A0Cybernetics/ID-01/Documents/buildGuidePictures/electronics1.jpg

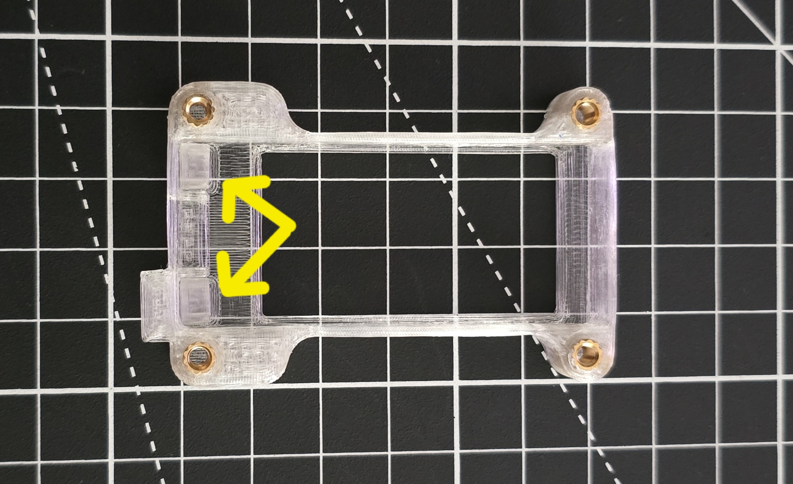
Documents/buildGuidePictures/electronics1.jpg
