A0Cybernetics/ID-01/Documents/buildGuidePictures/electronics4.jpg

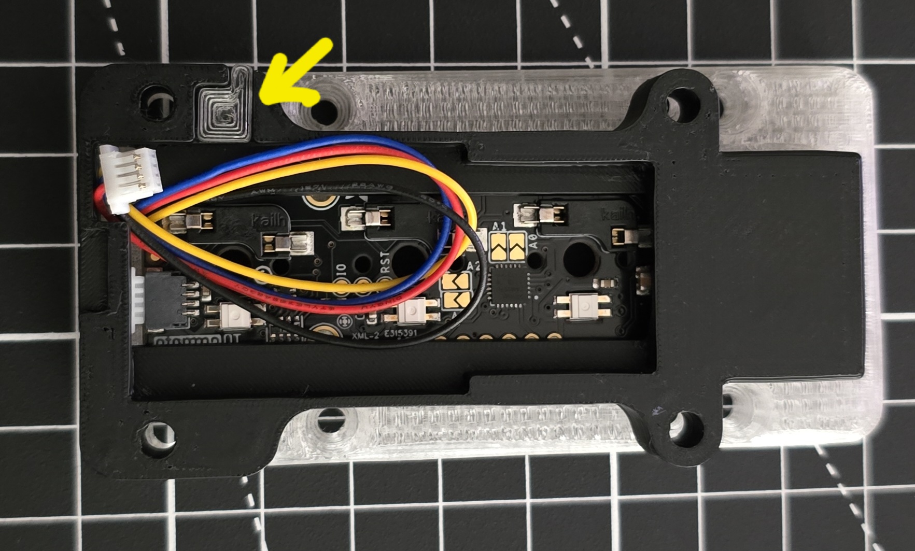
Documents/buildGuidePictures/electronics4.jpg
