A0Cybernetics/ID-01/Documents/buildGuidePictures/electronics5.jpg

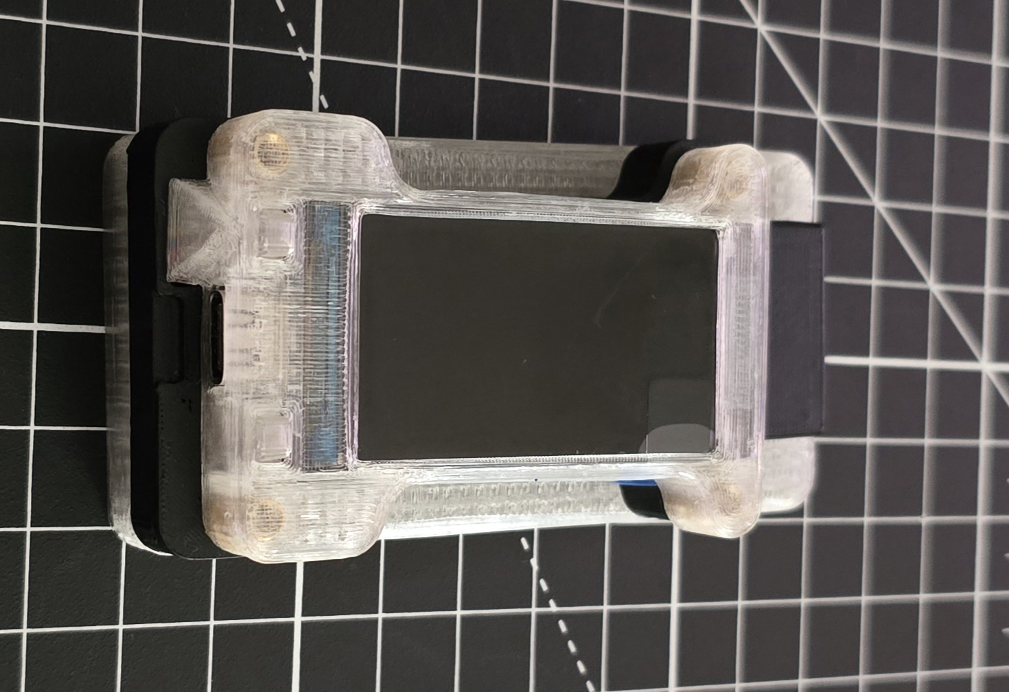
Documents/buildGuidePictures/electronics5.jpg
