A0Cybernetics/ID-01/Documents/buildGuidePictures/electronics6.jpg

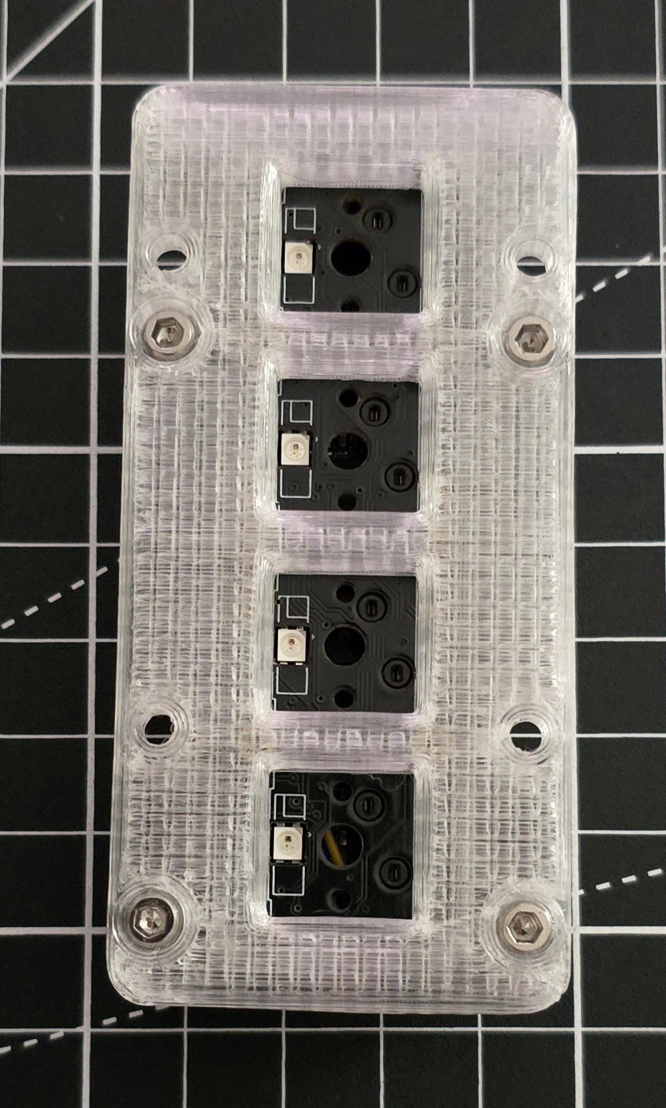
Documents/buildGuidePictures/electronics6.jpg
