A0Cybernetics/ID-01/Documents/READMEPics/led.jpg

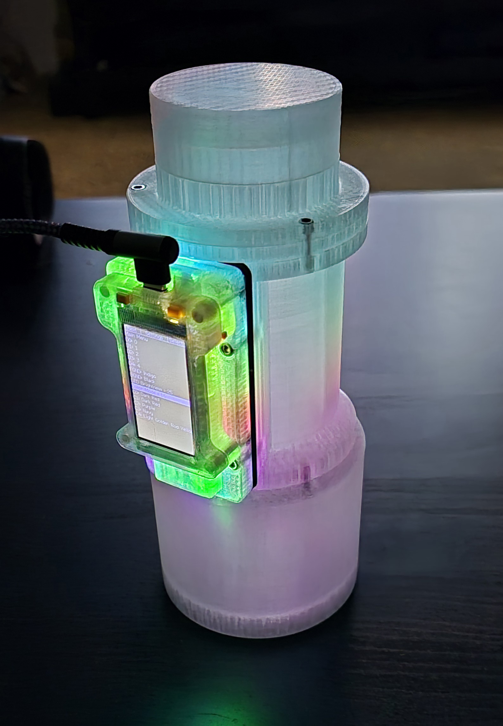
Documents/READMEPics/led.jpg
