A0Cybernetics/ID-01/3DModels/V1.0/Adapters-MFleshlight/endPieceFleshlightV1.0-67mm.FCStd

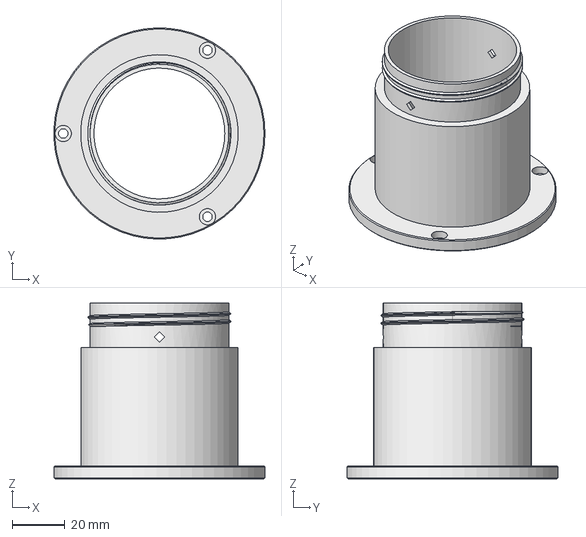
[picture p28: CAD file, 2024-03-15]
3DModels/V1.0/Adapters-MFleshlight/endPieceFleshlightV1.0-67mm.FCStd
80.3 x 80.4 x 67.0 mm
