A0Cybernetics/ID-01/3DModels/V1.0/Buttons/resetButtonV1.0.FCStd

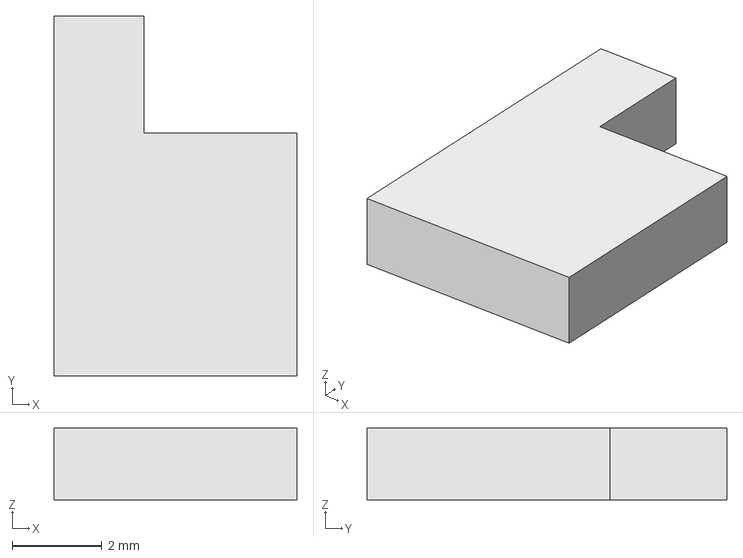
[picture p29: CAD file, 2024-03-15]
3DModels/V1.0/Buttons/resetButtonV1.0.FCStd
5.40 x 8.00 x 1.60 mm
