A0Cybernetics/ID-01/3DModels/V1.0/KeyPlateSpacers/keyPlateSpacerV1.0-1mm.FCStd

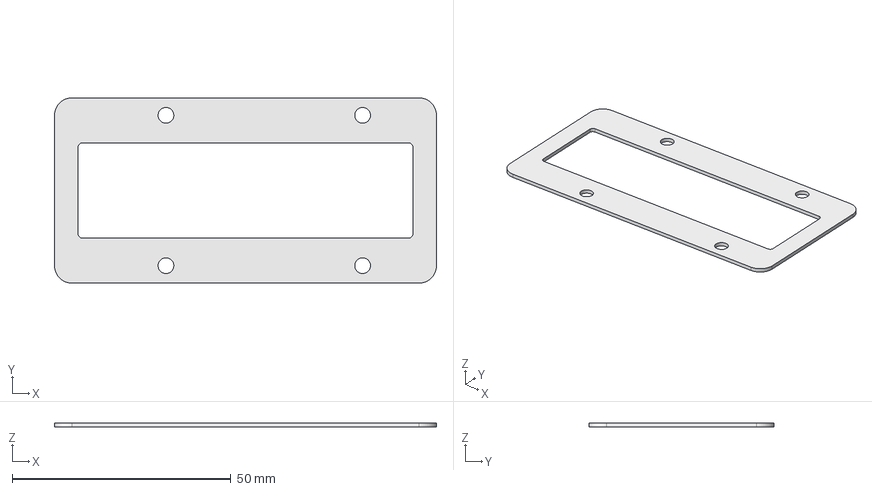
[picture p30: CAD file, 2024-03-15]
3DModels/V1.0/KeyPlateSpacers/keyPlateSpacerV1.0-1mm.FCStd
87.4 x 42.4 x 1.00 mm
