A0Cybernetics/ID-01/3DModels/V1.0/Adapters-FleshlightEndCaps/flEndCapV1.0.FCStd

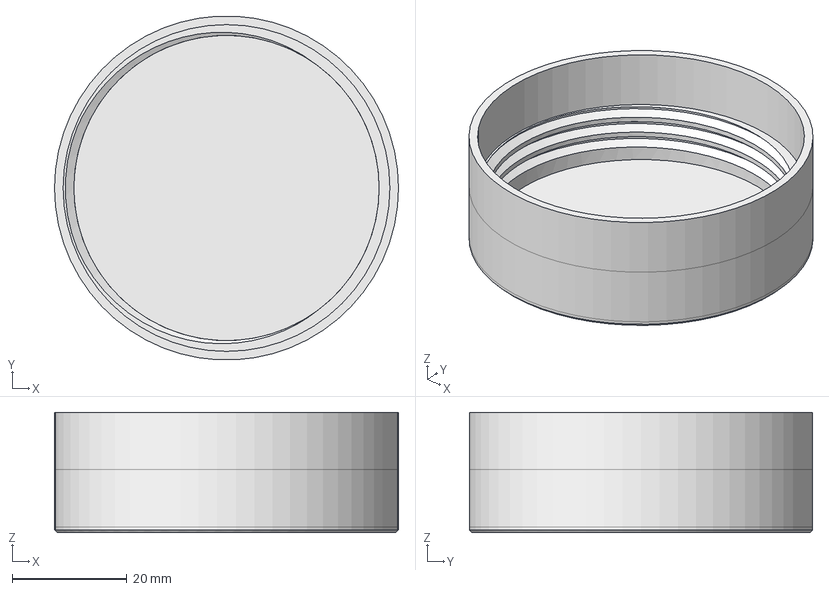
[picture p31: CAD file, 2024-03-15]
3DModels/V1.0/Adapters-FleshlightEndCaps/flEndCapV1.0.FCStd
60.0 x 59.9 x 21.0 mm
