A0Cybernetics/ID-01/3DModels/V1.0/KeyPlateSpacers/keyPlateSpacerV1.0-2mm.FCStd

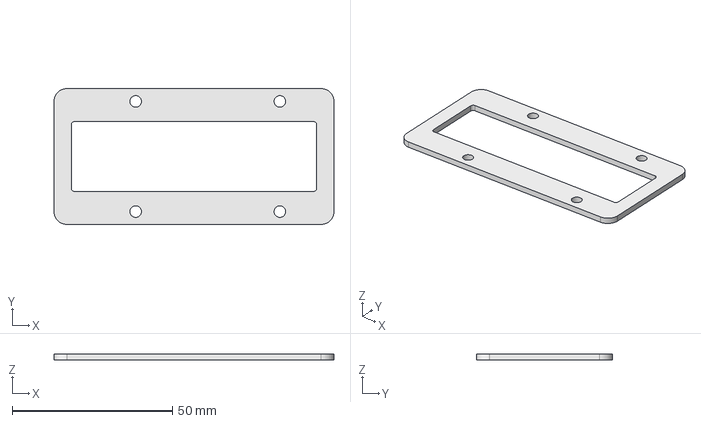
[picture p32: CAD file, 2024-03-15]
3DModels/V1.0/KeyPlateSpacers/keyPlateSpacerV1.0-2mm.FCStd
87.4 x 42.4 x 2.00 mm
