A0Cybernetics/ID-01/3DModels/V1.0/Stabilizers/stabilizerV1.0-50mm.FCStd

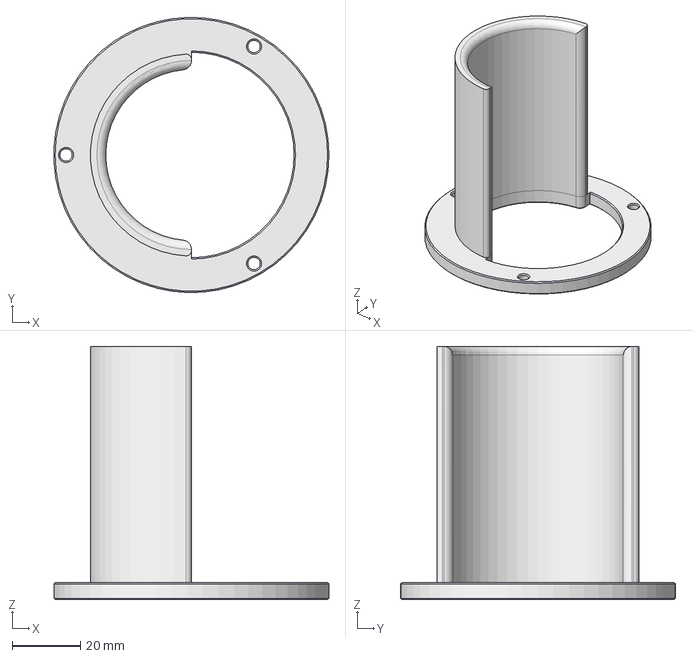
[picture p33: CAD file, 2024-03-15]
3DModels/V1.0/Stabilizers/stabilizerV1.0-50mm.FCStd
80.3 x 80.4 x 74.0 mm
