A0Cybernetics/ID-01/Documents/buildGuidePictures/adjustment2.jpg

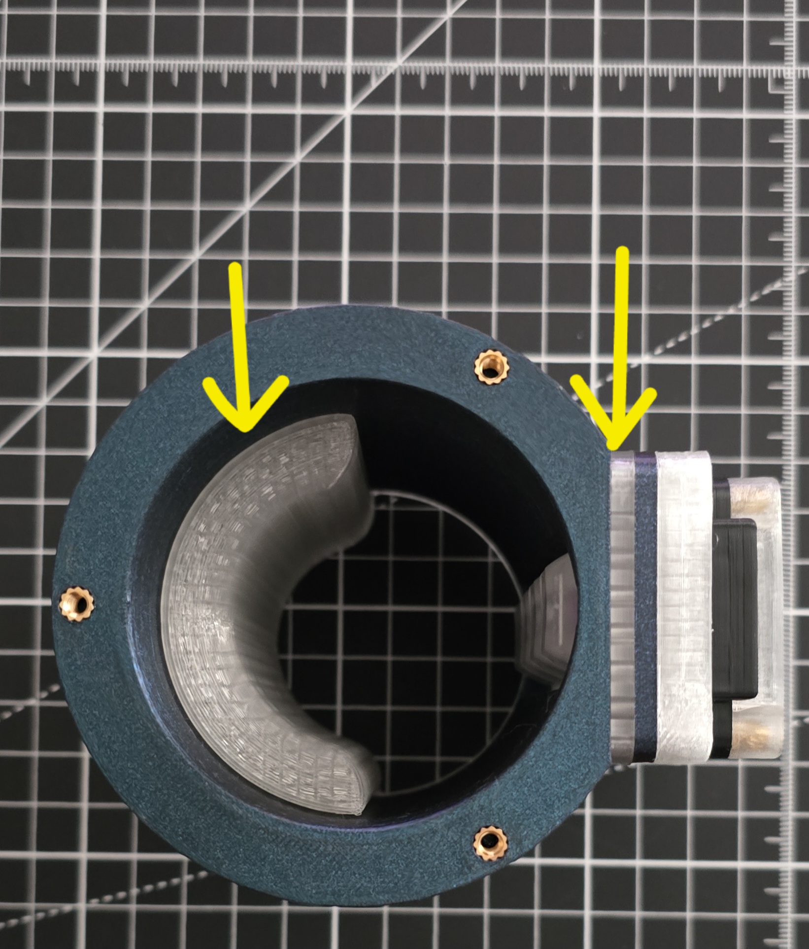
Documents/buildGuidePictures/adjustment2.jpg
