A0Cybernetics/ID-01/Documents/buildGuidePictures/adjustmet1.jpg

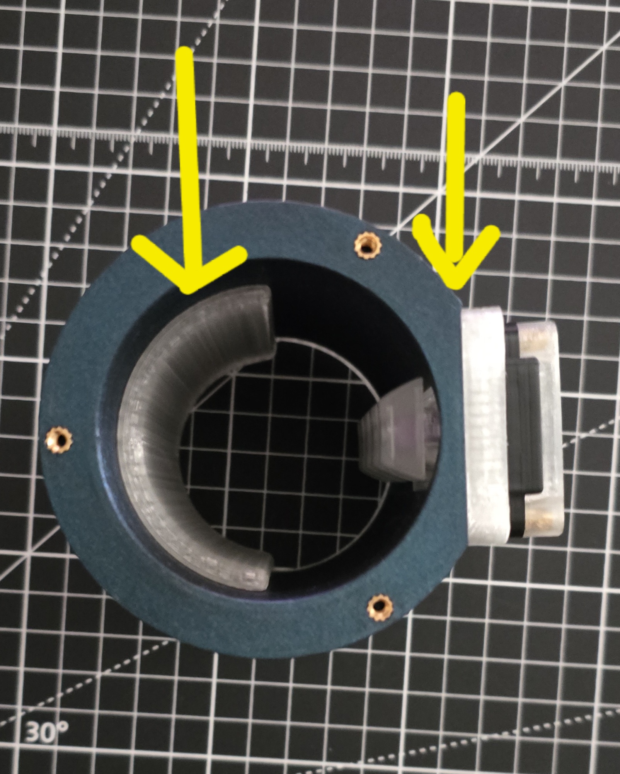
Documents/buildGuidePictures/adjustmet1.jpg
