A0Cybernetics/ID-01/Documents/buildGuidePictures/firmware1.png

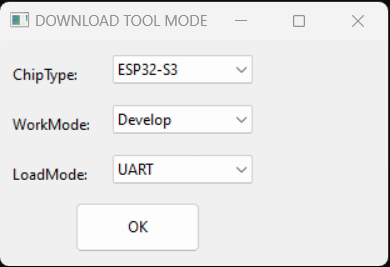
Documents/buildGuidePictures/firmware1.png
