A0Cybernetics/ID-01/Documents/buildGuidePictures/firmware2.png

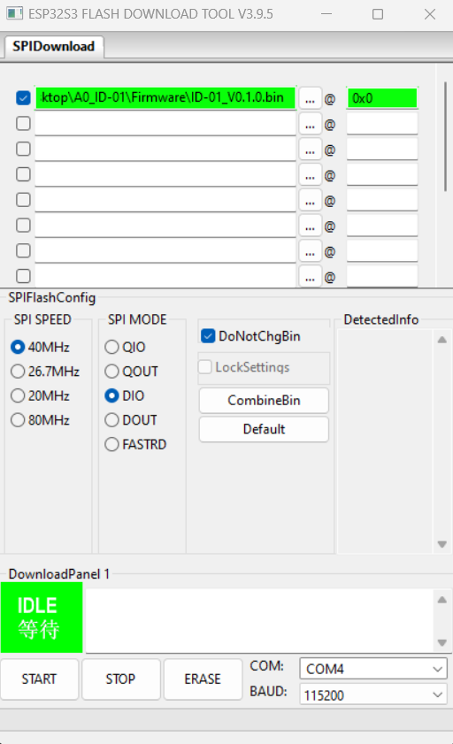
Documents/buildGuidePictures/firmware2.png
