A0Cybernetics/ID-01/Documents/buildGuidePictures/firmware3.png

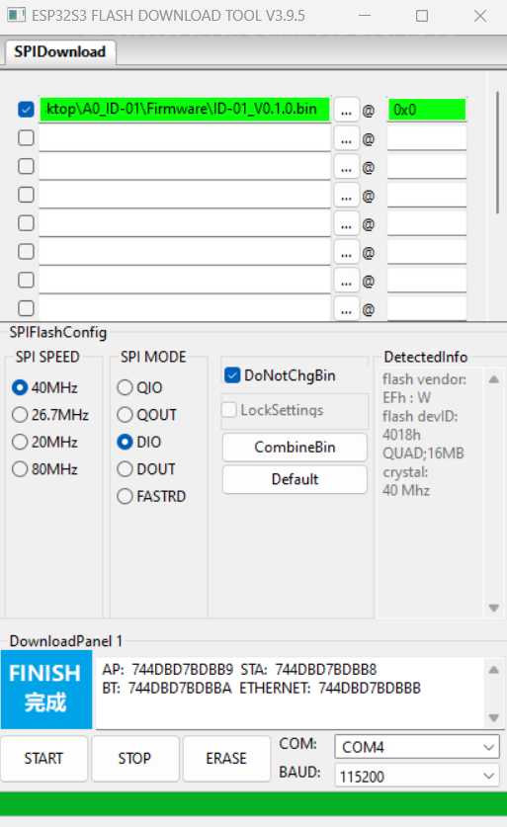
Documents/buildGuidePictures/firmware3.png
