A0Cybernetics/ID-01/Documents/buildGuidePictures/housing1.jpg

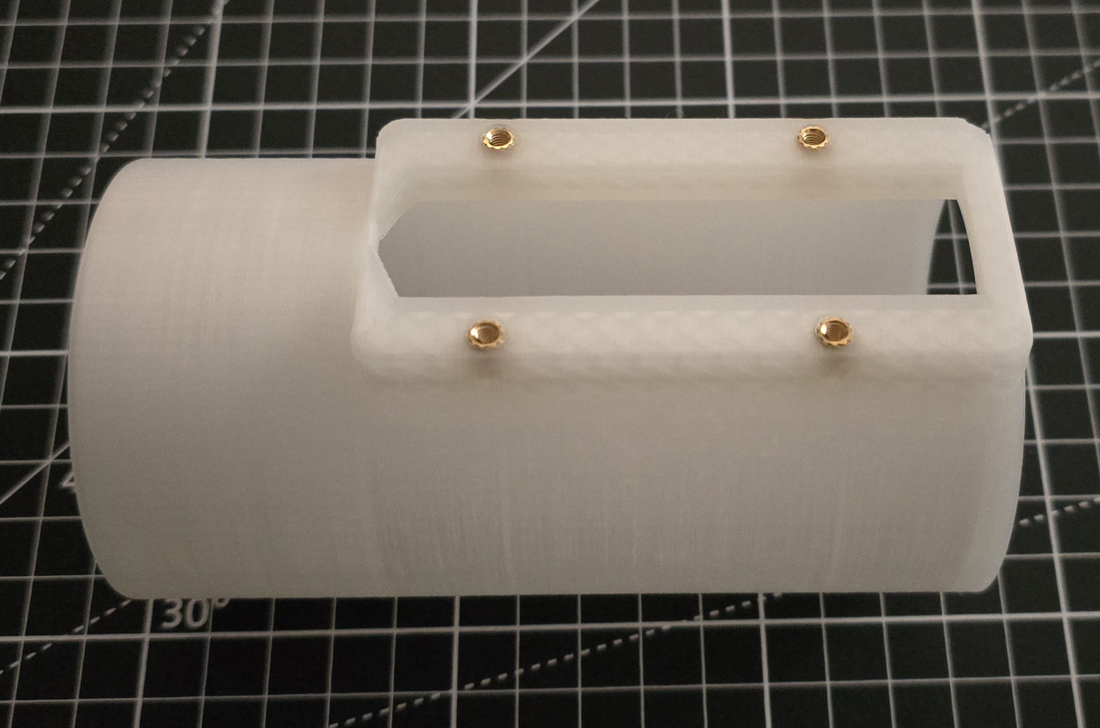
Documents/buildGuidePictures/housing1.jpg
