A0Cybernetics/ID-01/Documents/buildGuidePictures/housing2.jpg

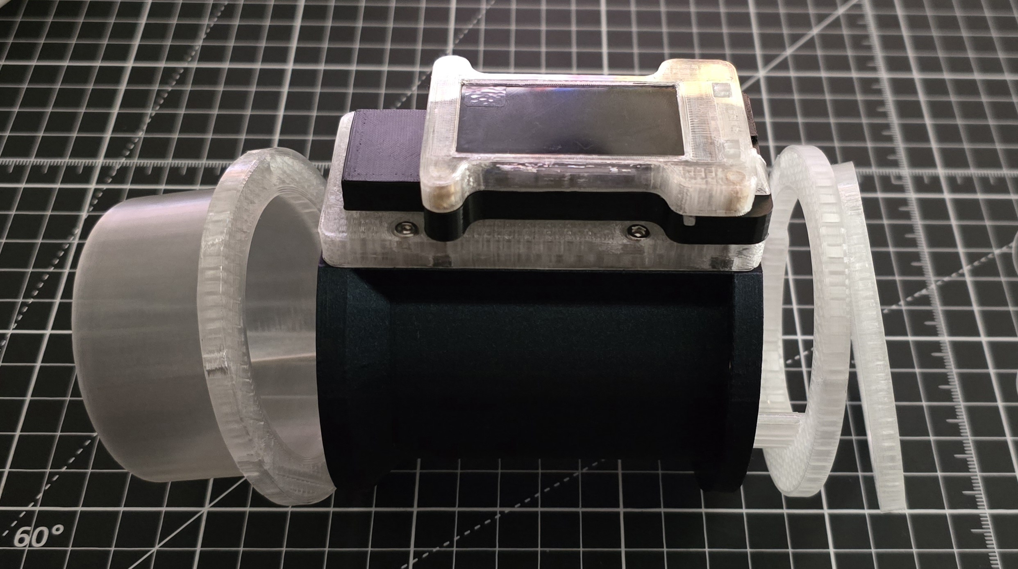
Documents/buildGuidePictures/housing2.jpg
