A0Cybernetics/ID-01/Documents/buildGuidePictures/housing3.jpg

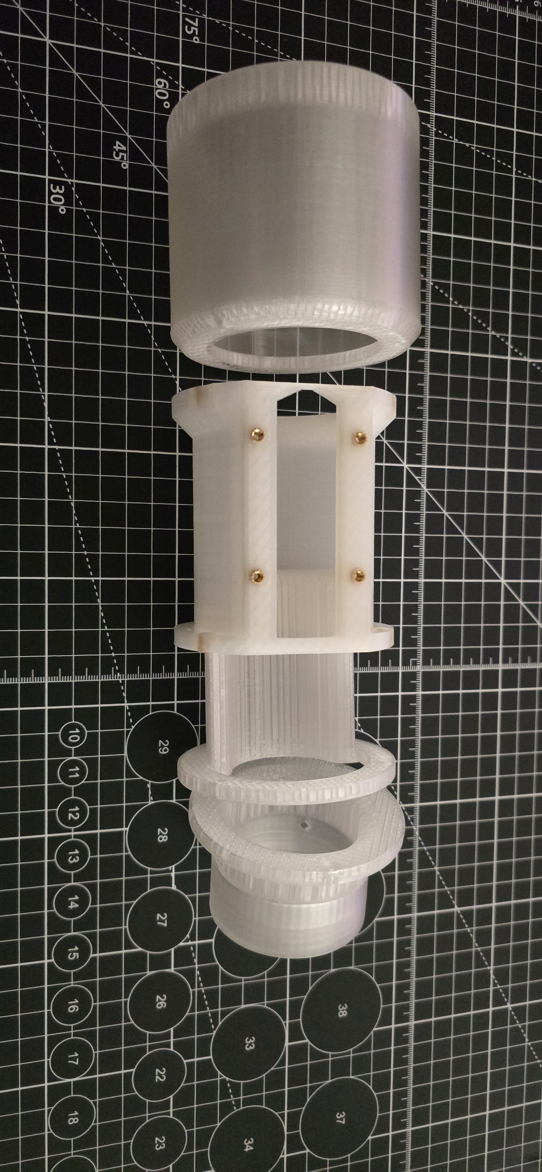
Documents/buildGuidePictures/housing3.jpg
