A0Cybernetics/ID-01/Documents/buildGuidePictures/housing5.jpg

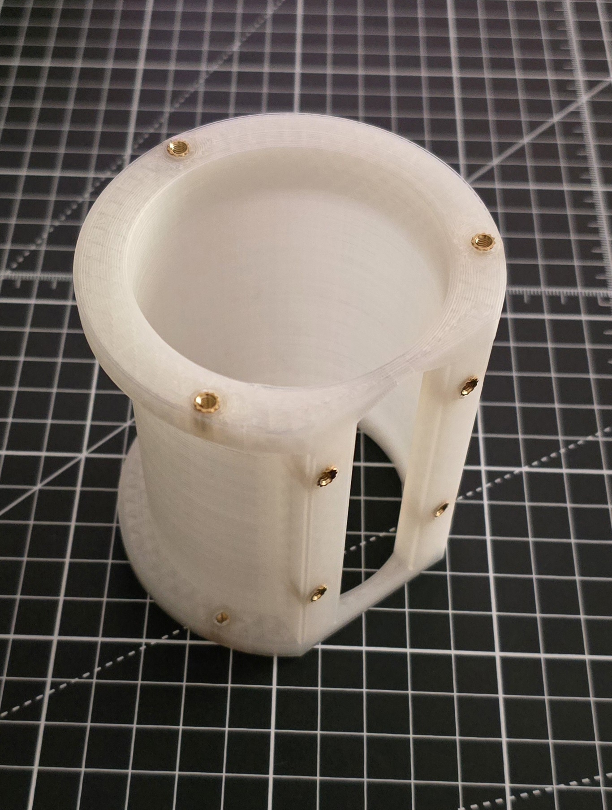
Documents/buildGuidePictures/housing5.jpg
