A0Cybernetics/ID-01/Documents/buildGuidePictures/housing6.jpg

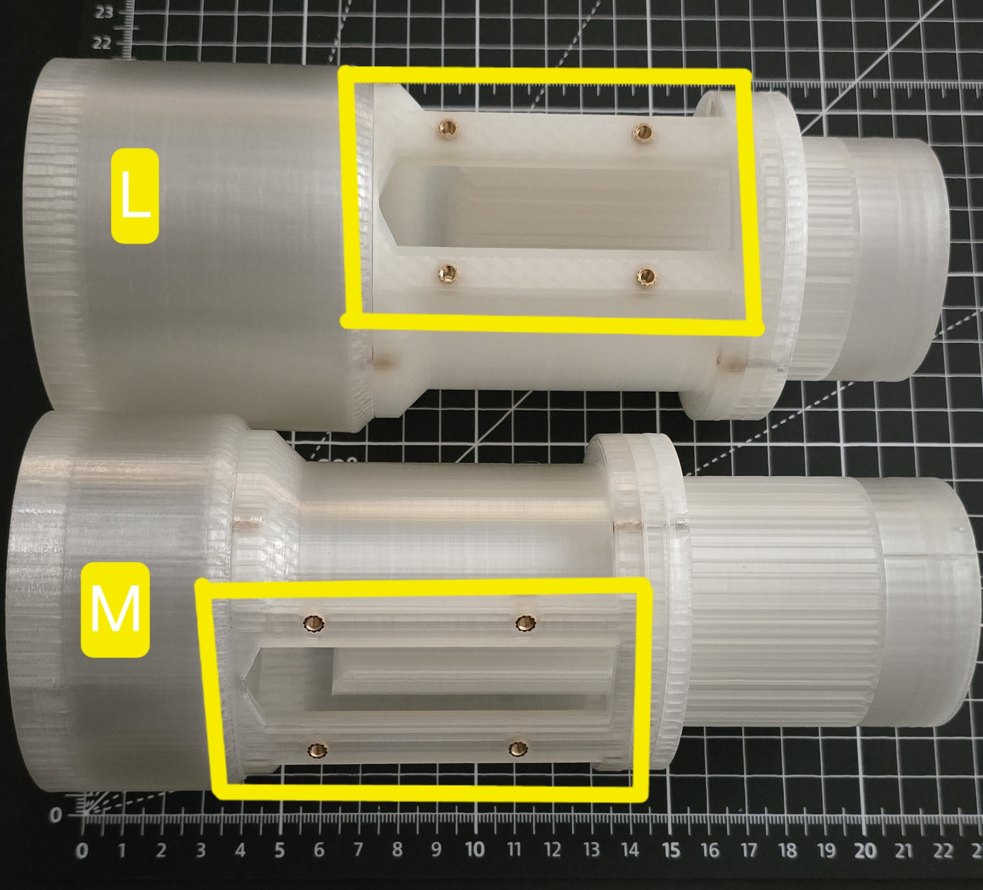
Documents/buildGuidePictures/housing6.jpg
