A0Cybernetics/ID-01/Documents/buildGuidePictures/operation1.jpg

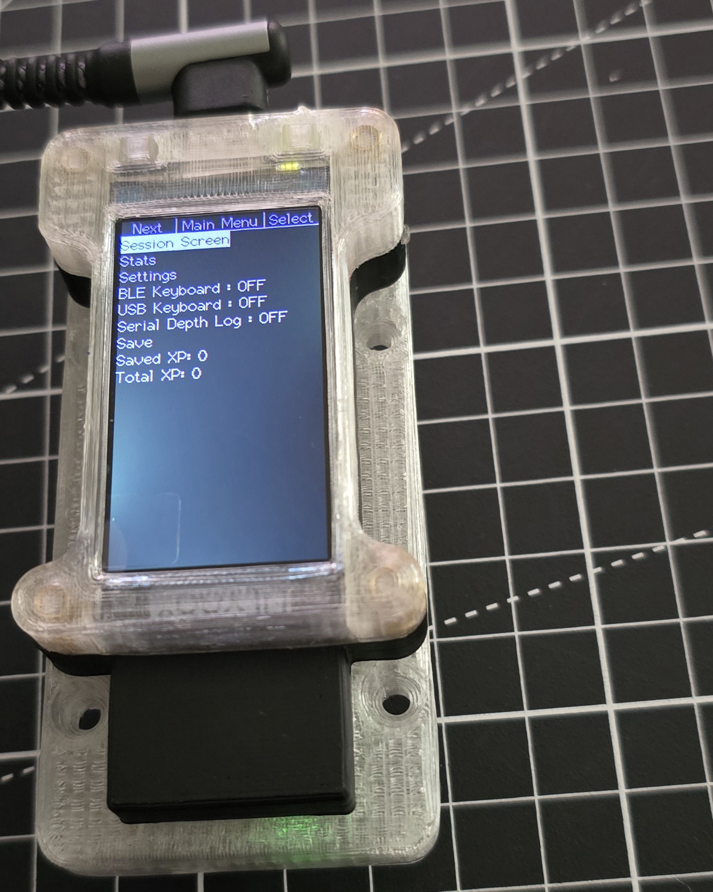
Documents/buildGuidePictures/operation1.jpg
