A0Cybernetics/ID-01/Documents/buildGuidePictures/operation3.jpg

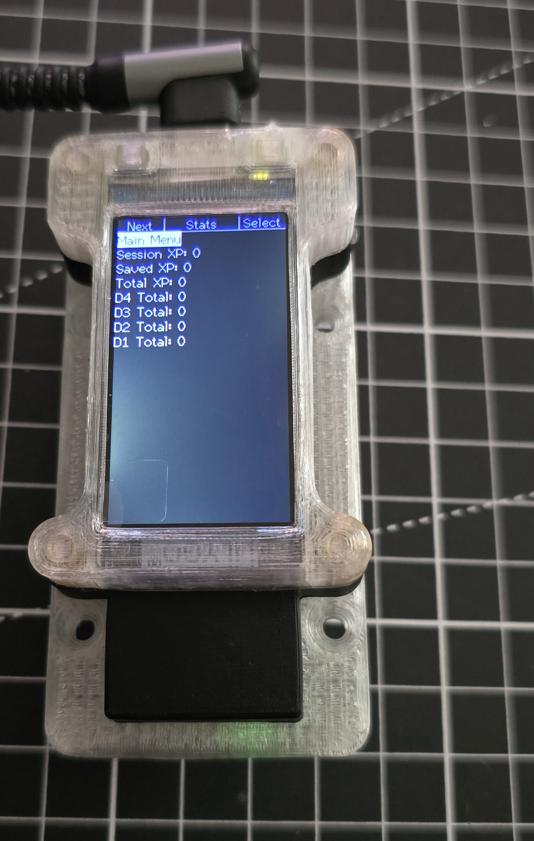
Documents/buildGuidePictures/operation3.jpg
