A0Cybernetics/ID-01/Documents/buildGuidePictures/operation4.jpg

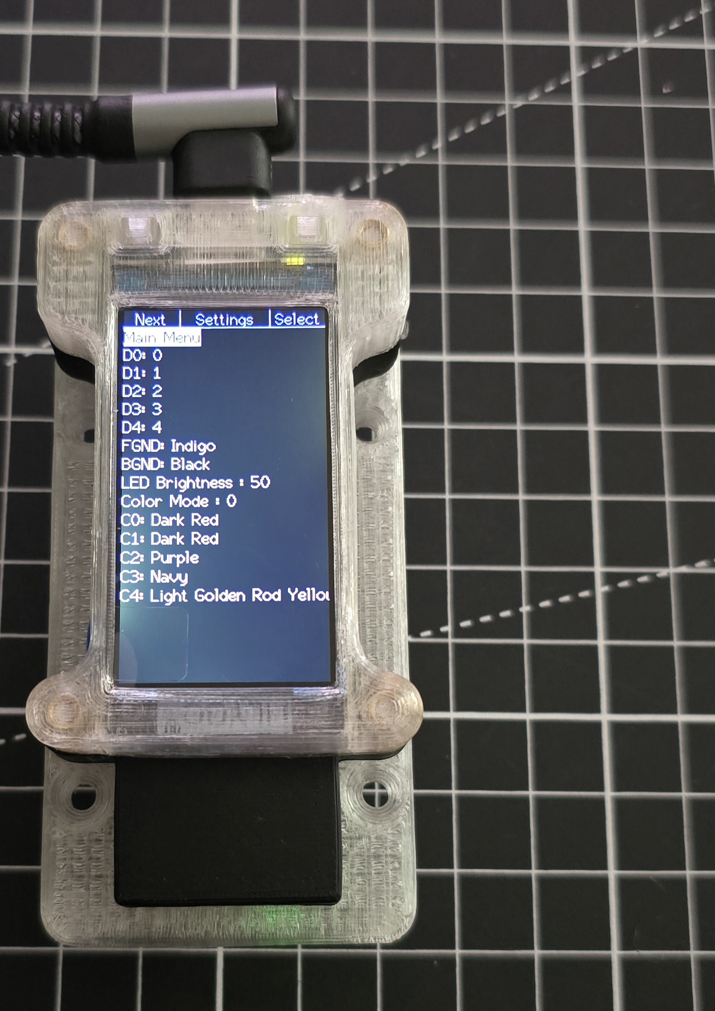
Documents/buildGuidePictures/operation4.jpg
